Toglefritz/Brine/brine_app/assets/bluetooth_error.png

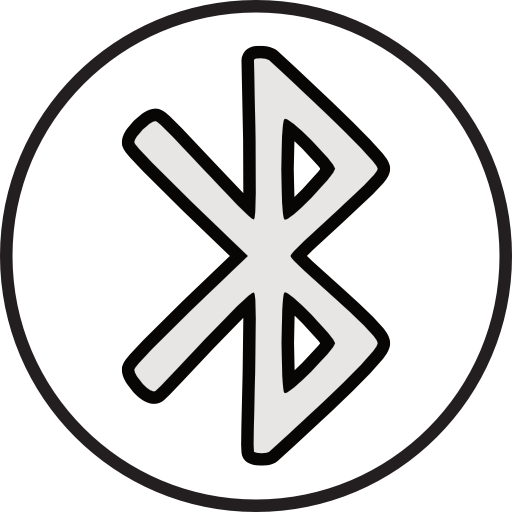
brine_app/assets/bluetooth_error.png
