Toglefritz/Brine/brine_app/assets/google.png

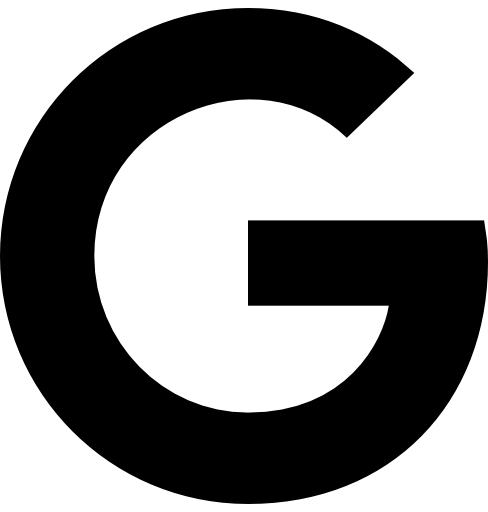
brine_app/assets/google.png
