Toglefritz/Brine/brine_store_listings/play_store/Brine Store Screenshots/Phone - Low Battery - Light Theme.png

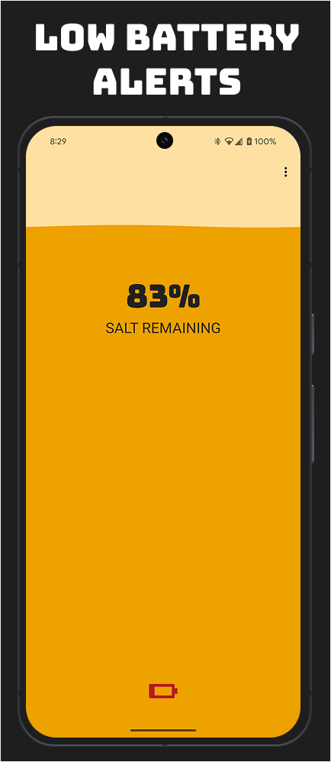
brine_store_listings/play_store/Brine Store Screenshots/Phone - Low Battery - Light Theme.png
