Toglefritz/Brine/brine_store_listings/play_store/Brine Store Screenshots/Phone - Normal - Dark Theme.png

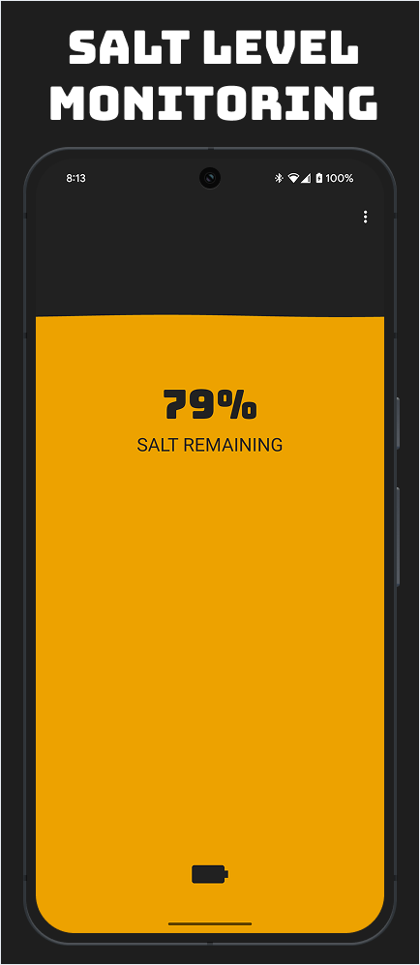
brine_store_listings/play_store/Brine Store Screenshots/Phone - Normal - Dark Theme.png
