Toglefritz/Brine/brine_store_listings/play_store/Brine Store Screenshots/Tablet - Low Salt - Light Theme.png

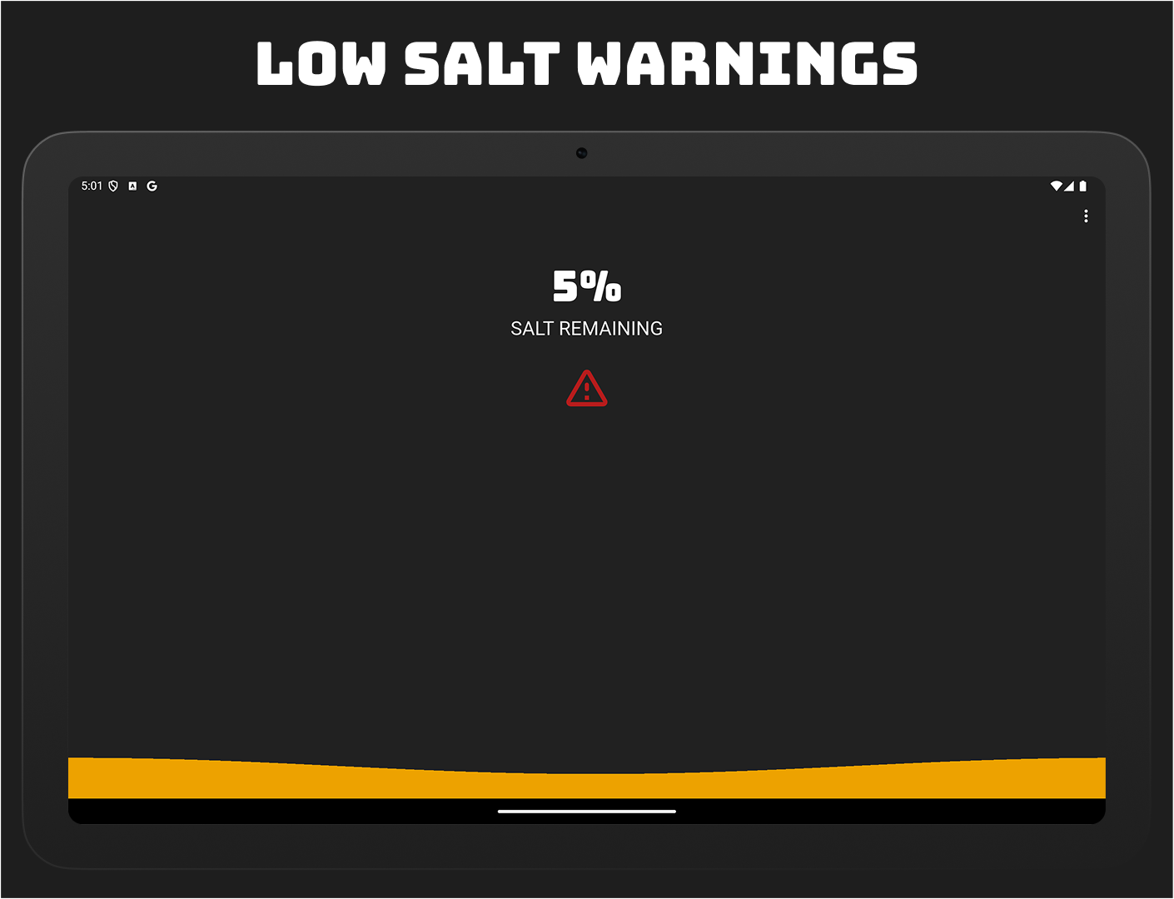
brine_store_listings/play_store/Brine Store Screenshots/Tablet - Low Salt - Light Theme.png
