Toglefritz/Brine/brine_store_listings/play_store/Brine Store Screenshots/Tablet - Normal - Dark Theme.png

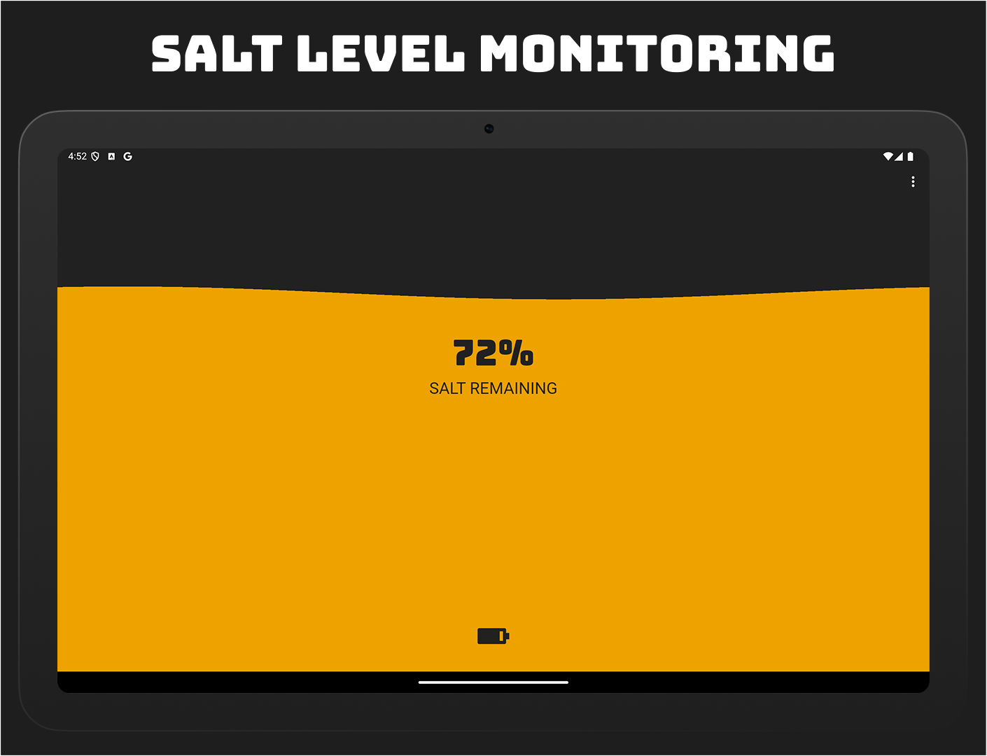
brine_store_listings/play_store/Brine Store Screenshots/Tablet - Normal - Dark Theme.png
