Toglefritz/Brine/brine_store_listings/play_store/feature_graphic.png

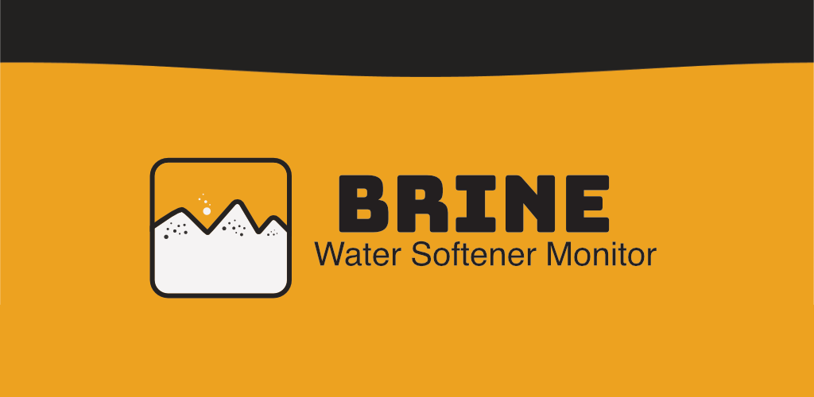
brine_store_listings/play_store/feature_graphic.png
