Toglefritz/Brine/brine_website/assets/hair.png

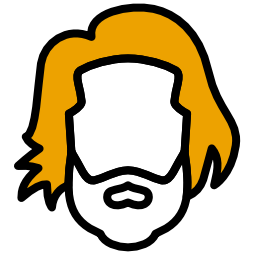
brine_website/assets/hair.png
