Toglefritz/Brine/brine_website/assets/hair_white.png

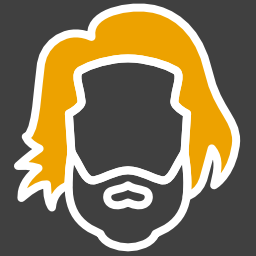
brine_website/assets/hair_white.png
