Toglefritz/Brine/brine_website/assets/numeral_2.png

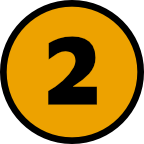
brine_website/assets/numeral_2.png
