Toglefritz/Brine/brine_website/assets/soap_hands.png

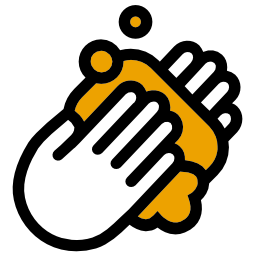
brine_website/assets/soap_hands.png
