Toglefritz/Brine/brine_website/assets/soap_hands_white.png

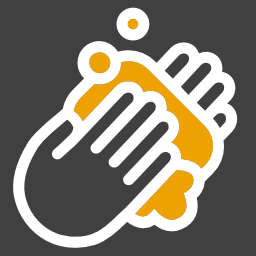
brine_website/assets/soap_hands_white.png
