Toglefritz/Brine/brine_website/assets/socks.png

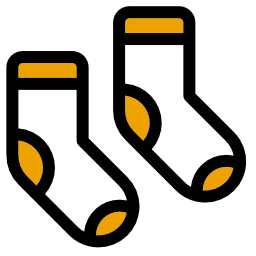
brine_website/assets/socks.png
