Toglefritz/Brine/brine_website/assets/socks_white.png

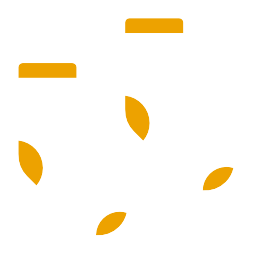
brine_website/assets/socks_white.png
