Toglefritz/Brine/brine_website/assets/brine_parts_map.png

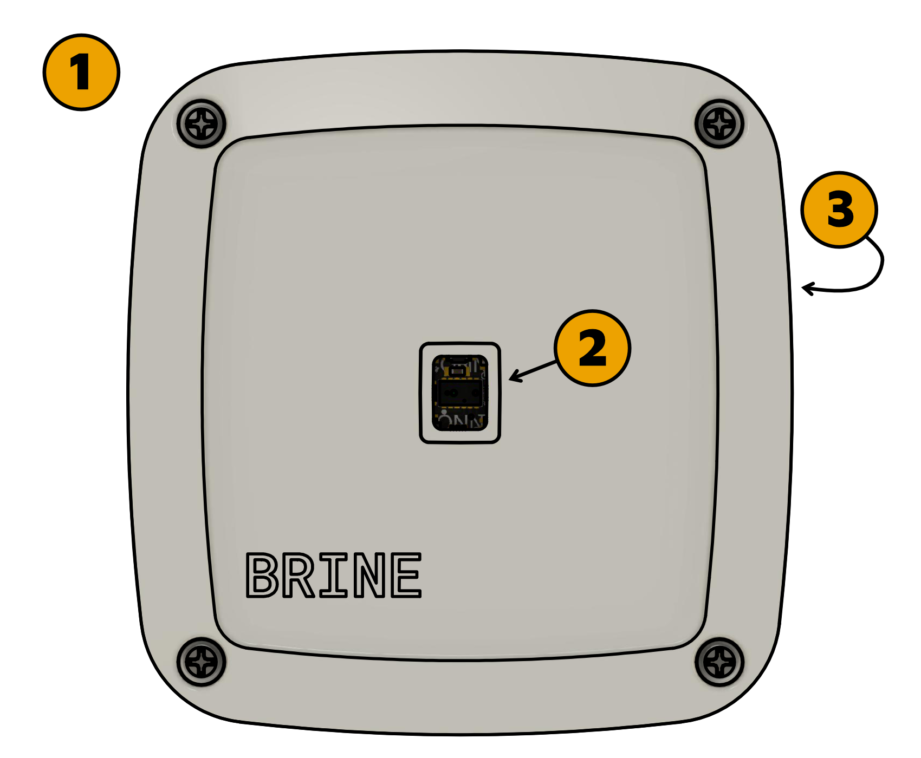
brine_website/assets/brine_parts_map.png
