Toglefritz/Brine/brine_firmware/test/test_WS2812BLED/test_WS2812BLED.cpp

#include "test_WS2812BLED.h"
#include <WS2812BLED.h>
#include <unity.h>

/*
 *  This test file tests the WS2812BLED class. The WS2812BLED class is a singleton class
 * that controls WS2812B RGB LEDs connected to a GPIO pin. The WS2812BLED class provides
 * methods for color control, brightness adjustment, and various effects including
 * turnOn(), turnOff(), setColor(), setBrightness(), blink(), rainbow(), and breathe().
 * This test file tests the functionality of the WS2812BLED class by controlling the LED
 * and asking the user to verify the visual output.
 *
 * Hardware Setup for XIAO ESP32-S3:
 * - Connect WS2812B VCC to 3.3V or 5V
 * - Connect WS2812B GND to GND
 * - Connect WS2812B DIN to GPIO2 (safer than GPIO1 which can conflict with UART)
 *
 *  Run this test with the command `pio test --filter test_WS2812BLED`.
 */

// Define number of LEDs for testing
#define NUM_LEDS 1

// WS2812B_DATA_PIN is defined in the library header (default: GPIO1/D0/A0 for XIAO ESP32-S3)
// Can be overridden with build flags if needed

/**
 * @brief Prints an initial test setup message.
*/
void show_test_setup_message(void) {
    TEST_IGNORE_MESSAGE("Please observe the LED during testing for visual verification.");
}

/**
 * @brief Tests initialization of the WS2812B LED.
 */
void test_led_initialization(void) { 
    test_ws2812b_initialization(NUM_LEDS); 
}

/**
 * @brief Tests turning the LED on.
 */
void test_led_turn_on(void) {
    test_ws2812b_turn_on();
    TEST_IGNORE_MESSAGE("LED should be ON (white). Verify visually.");
}

/**
 * @brief Tests turning off the LED.
 */
void test_led_turn_off(void) {
    test_ws2812b_turn_off();
    TEST_IGNORE_MESSAGE("LED should be OFF. Verify visually.");
}

/**
 * @brief Tests RGB color setting.
 */
void test_color_control_rgb(void) {
    test_ws2812b_set_color_rgb();
    TEST_IGNORE_MESSAGE("LED should have cycled through Red -> Green -> Blue -> White. Verify visually.");
}

/**
 * @brief Tests CRGB color setting.
 */
void test_color_control_crgb(void) {
    test_ws2812b_set_color_crgb();
    TEST_IGNORE_MESSAGE("LED should have shown various colors including a custom purple. Verify visually.");
}

/**
 * @brief Tests brightness control.
 */
void test_brightness_control(void) {
    test_ws2812b_brightness();
    TEST_IGNORE_MESSAGE("LED should have shown different brightness levels. Verify visually.");
}

/**
 * @brief Tests blink effect.
 */
void test_blink_effect(void) {
    test_ws2812b_blink_effect();
    TEST_IGNORE_MESSAGE("LED should have blinked green rapidly for 3 seconds. Verify visually.");
}

/**
 * @brief Tests rainbow effect.
 */
void test_rainbow_effect(void) {
    test_ws2812b_rainbow_effect();
    TEST_IGNORE_MESSAGE("LED should have shown a smooth rainbow cycle for 2 seconds. Verify visually.");
}

/**
 * @brief Tests breathing effect.
 */
void test_breathing_effect(void) {
    test_ws2812b_breathing_effect();
    TEST_IGNORE_MESSAGE("LED should have shown a blue breathing effect for 3 seconds. Verify visually.");
}

/**
 * @brief Tests color retrieval.
 */
void test_color_retrieval(void) {
    test_ws2812b_get_color();
}

/**
 * @brief Prints a message when the test is complete.
*/
void show_test_complete_message(void) {
    TEST_IGNORE_MESSAGE("All tests completed. LED should be OFF.");
}

/**
 * @brief Initializes the test environment and runs the Unity test framework.
 *
 * This function runs all WS2812B LED tests with visual verification instructions
 * provided through TEST_IGNORE_MESSAGE calls that appear in PlatformIO test output.
 */
void setup() {
    // Add startup delay to ensure system stability
    delay(2000);
    
    // Start the Unity test framework
    UNITY_BEGIN();

    // Add initial setup message
    RUN_TEST(show_test_setup_message);
     
    // Basic functionality tests
    RUN_TEST(test_led_initialization);
    delay(500);
    
    RUN_TEST(test_led_turn_on);
    delay(2000);
    
    RUN_TEST(test_led_turn_off);
    delay(1000);

    // Color control tests
    RUN_TEST(test_color_control_rgb);
    delay(2000);
    
    RUN_TEST(test_color_control_crgb);
    delay(2000);

    // Brightness control test
    RUN_TEST(test_brightness_control);
    delay(2000);

    // Effect tests
    RUN_TEST(test_blink_effect);
    delay(1000);
    
    RUN_TEST(test_rainbow_effect);
    delay(1000);
    
    RUN_TEST(test_breathing_effect);
    delay(1000);

    // Data integrity test
    RUN_TEST(test_color_retrieval);

    // Final cleanup
    WS2812BLED::getInstance().turnOff();

    // Add test completion message
    RUN_TEST(show_test_complete_message);

    // End the Unity test framework
    UNITY_END();
}

void loop() {
    // Do nothing - all tests run in setup()
}
